call286/AmigaSID/Hardware/original/1.jpg

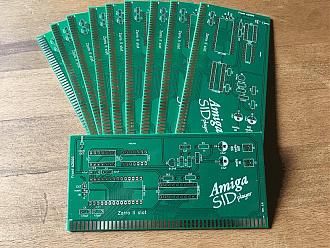
Hardware/original/1.jpg
