call286/AmigaSID/Hardware/original/2.jpg

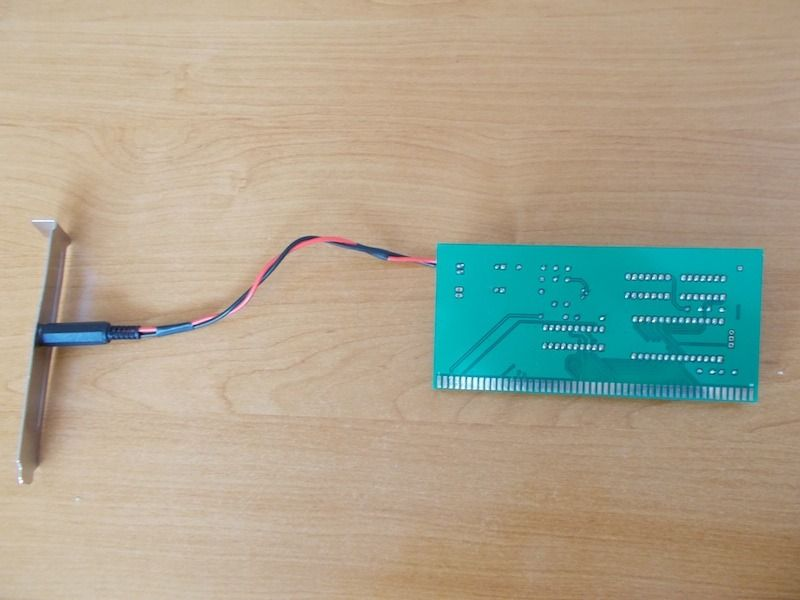
Hardware/original/2.jpg
