call286/AmigaSID/Hardware/original/3.jpg

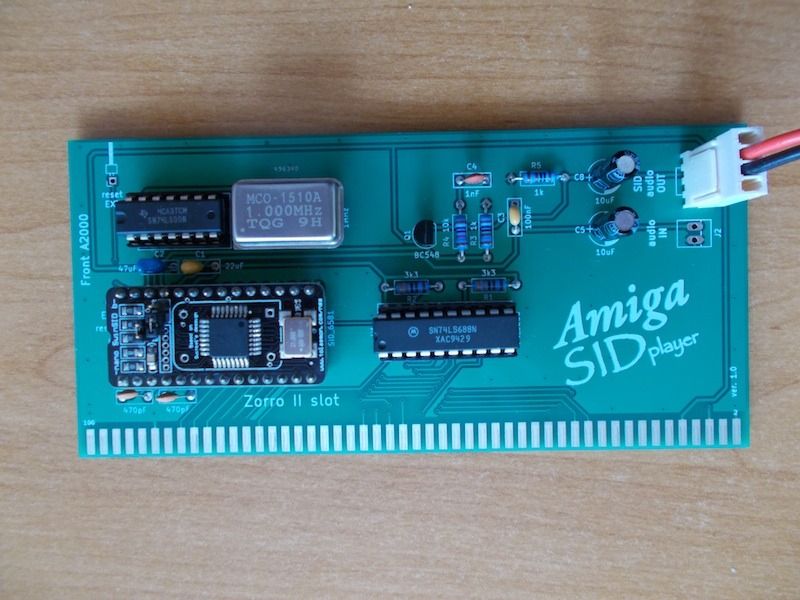
Hardware/original/3.jpg
