call286/AmigaSID/Hardware/original/4.jpg

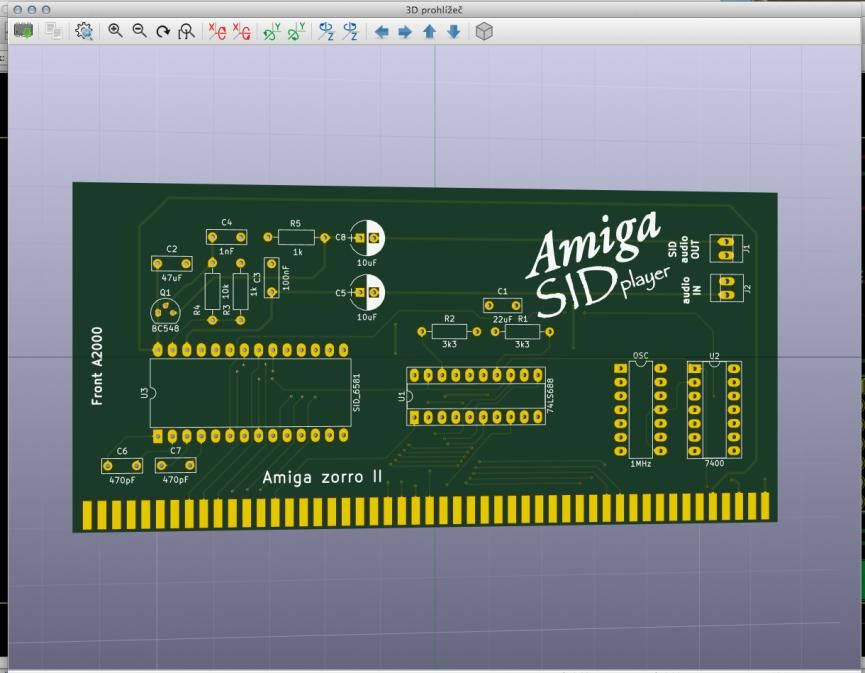
Hardware/original/4.jpg
